calcpsu/cptibp8/simulation/model.asc

C1: cap; 940µ
D1: schottky; 1N5817
D2: schottky; 1N5817
D3: schottky; 1N5817
D4: schottky; 1N5817
I1: current; 0.25
R4: res; 1
V1: voltage; SINE(0 7 50)
Named nets: 0, vrect
.tran 0 1.0 0 startup
